Thomas49600/Flippy/V8.2_Seven_Segment_Display/main/data/A.jpg

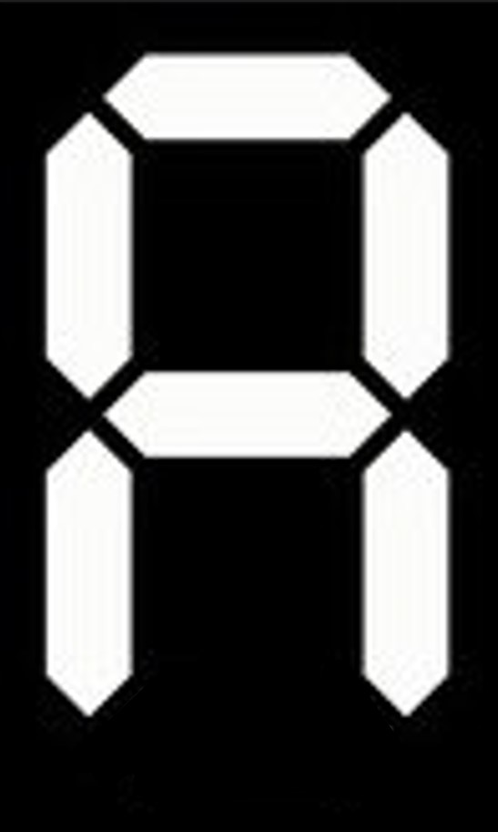
V8.2_Seven_Segment_Display/main/data/A.jpg
