Thomas49600/Flippy/V8.2_Seven_Segment_Display/main/data/h.jpg

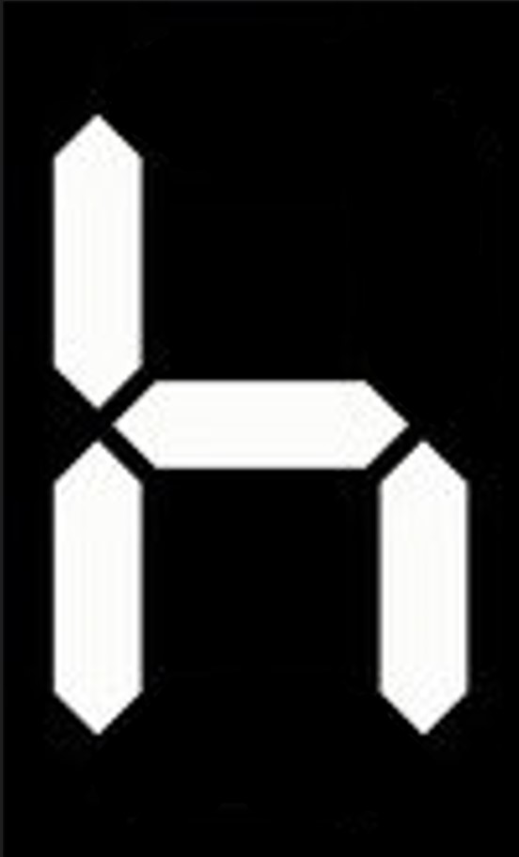
V8.2_Seven_Segment_Display/main/data/h.jpg
