Thomas49600/Flippy/V8.2_Seven_Segment_Display/main/main.ino

#include "wifi.h"
#include "counter.h"


void setup () {
  Serial.begin(115200); // start serial communication
  delay(10);

  setupWifi();
  delay(1000);
  setupCounter();
  setupCounterObjs();
}


void loop() {
  wifiChecks();
}
