Thomas49600/Flippy/V8.2_Seven_Segment_Display/main/modes.h

#ifndef MODE_H
#define MODE_H
#include <Arduino.h>  // Include Arduino functions like delay(), pinMode(), etc.
#include <ArduinoJson.h>

// Function prototypes (public)
void getModesJson(DynamicJsonDocument& doc);

#endif
